MOSH-Insa-Toulouse/2025-2026-4GP-Robinson-Podgorski/2. Kicad/kicad-flex-sensor/Modèles 3D/pin-header-female-double-2-54mm-different-pin-numbers-1.snapshot.2/10-Pin Header - Female - Double - 2.54mm.step

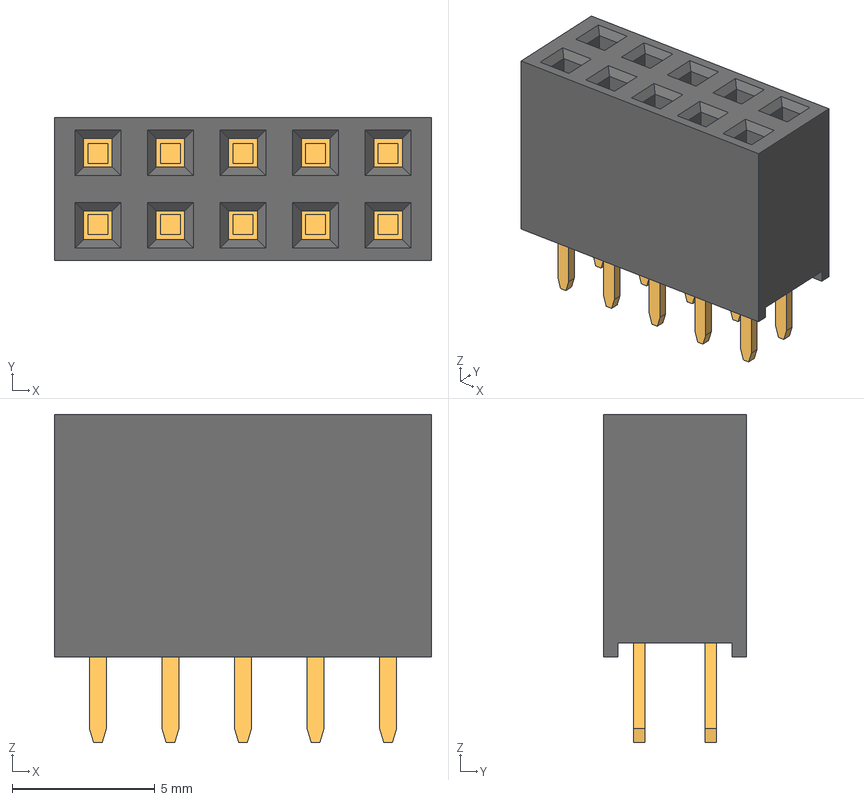
[picture p31: CAD file, 2026-02-17]
2. Kicad/kicad-flex-sensor/Modèles 3D/pin-header-female-double-2-54mm-different-pin-numbers-1.snapshot.2/10-Pin Header - Female - Double - 2.54mm.step
13.2 x 5.00 x 11.5 mm
