MOSH-Insa-Toulouse/2025-2026-4GP-Robinson-Podgorski/2. Kicad/Ressources moodle/pin-header-female-2-54mm-different-pin-numbers-1.snapshot.4/19-Pin Header - Female - 2.54mm.step

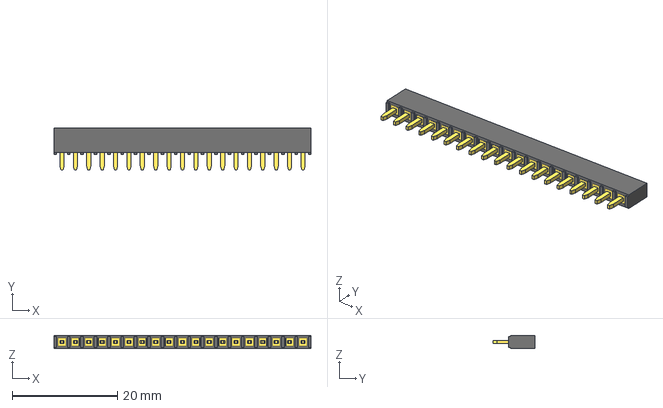
[picture p36: CAD file, 2026-02-20]
2. Kicad/Ressources moodle/pin-header-female-2-54mm-different-pin-numbers-1.snapshot.4/19-Pin Header - Female - 2.54mm.step
48.8 x 8.00 x 2.50 mm
