MOSH-Insa-Toulouse/2025-2026-4GP-Robinson-Podgorski/1. LTSpice/Capteur_graphite_complet.asc

C1: cap; 100n
C2: cap; 100n
C3: cap; 1p
C4: cap; 1µ
R1: res; 100k
R2: res; 1k
R3: res; 100k
R4: res; 1k
R5: res; 10k
U1: LTC1050
V1: voltage; 5
V2: voltage; SINE(0 325 50)
V3: voltage; PULSE(0 1 0.2 0.1 0.1 20)
X1: Capteur_graphite
Named nets: 0, Vem, Vep, ADC
.tran 2
;ac dec 100 1 1G
.param G0 10n
.param G1 10n
.param R1 100k
